Beukhof-Techniek/ESP32-EnBaFu-Meter/images/breadboard03.jpg

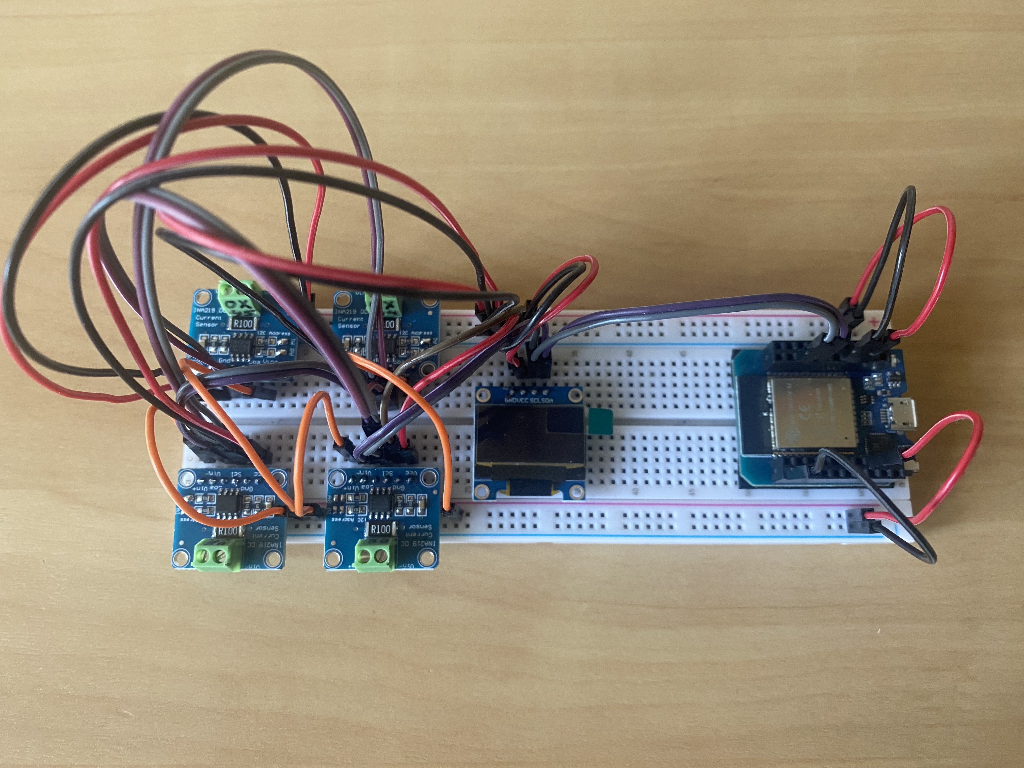
images/breadboard03.jpg
