Beukhof-Techniek/ESP32-EnBaFu-Meter/images/pcb_assembled.jpg

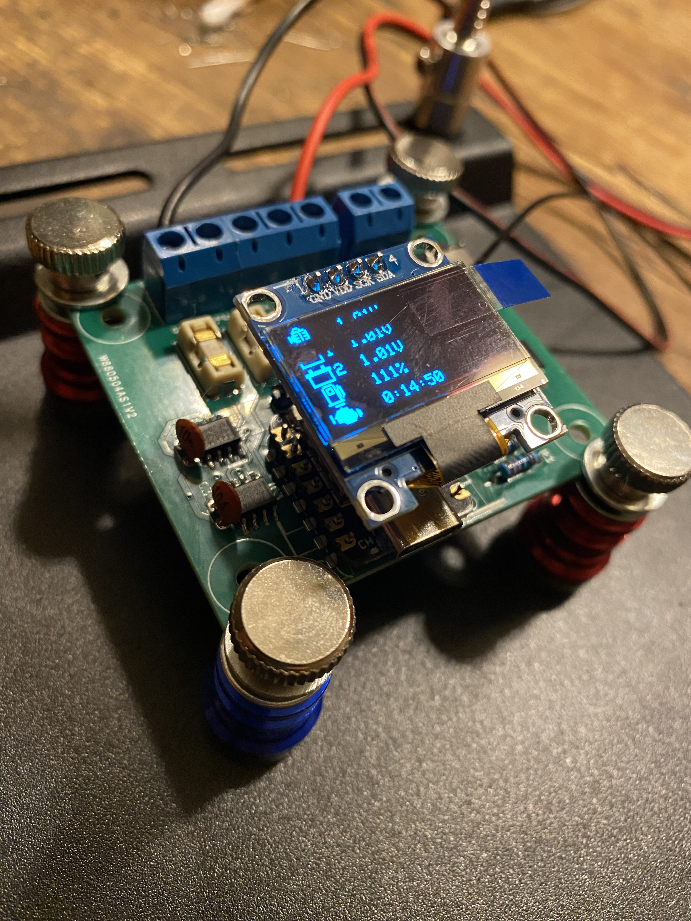
images/pcb_assembled.jpg
